madworm/IKEA-Samtid_mood-light/Docs/V027a_fuse.jpg

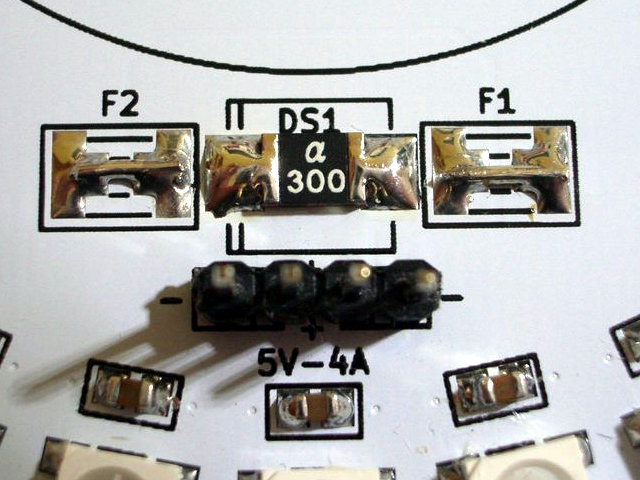
Docs/V027a_fuse.jpg
