madworm/IKEA-Samtid_mood-light/gerber_files/PNGs/IKEA-Samtid_mood-light__back_purple.png

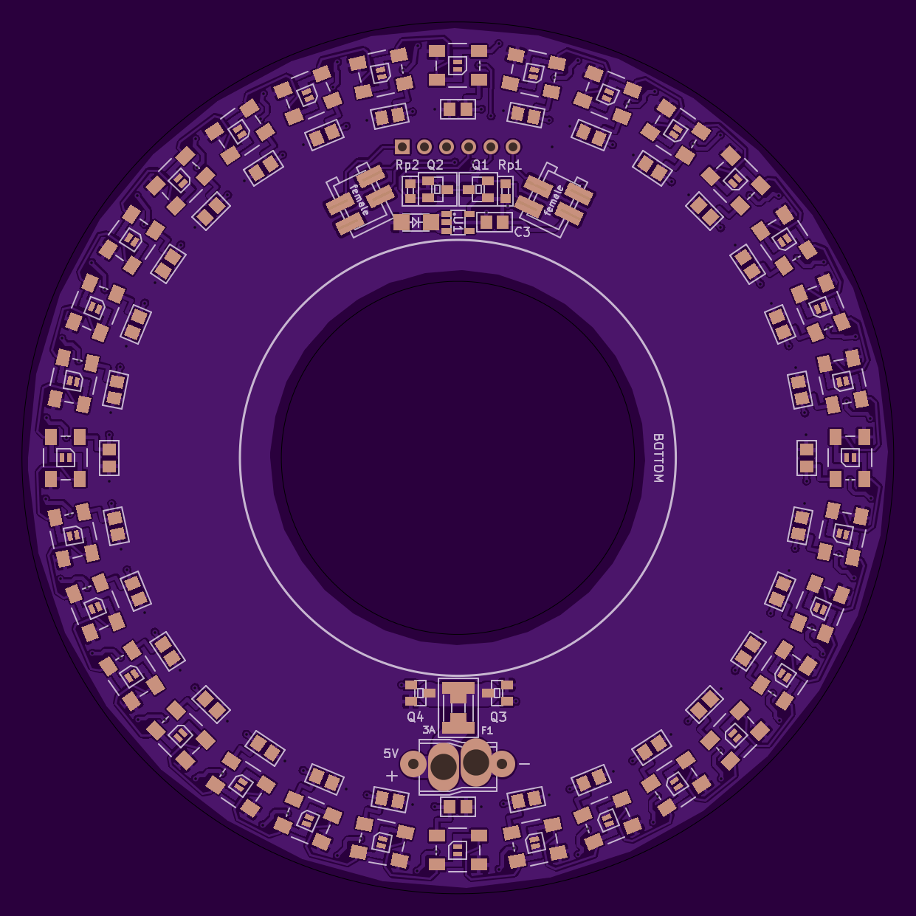
gerber_files/PNGs/IKEA-Samtid_mood-light__back_purple.png
