madworm/IKEA-Samtid_mood-light/gerber_files_ctrl-board/PNGs/IKEA-Samtid_mood-light_ctrl-board__front_purple.png

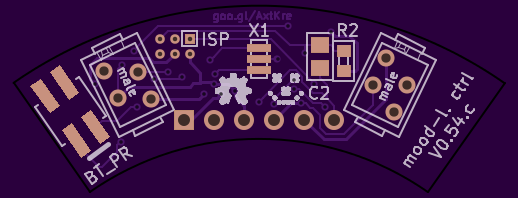
gerber_files_ctrl-board/PNGs/IKEA-Samtid_mood-light_ctrl-board__front_purple.png
