madworm/IKEA-Samtid_mood-light/gerber_files_esp8266-adapter/PNGs/IKEA-Samtid_mood-light_esp8266-adapter__back_purple.png

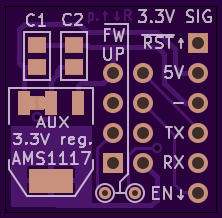
gerber_files_esp8266-adapter/PNGs/IKEA-Samtid_mood-light_esp8266-adapter__back_purple.png
